NNNILabs/CC-CV-Linear-Power-Supply/KiCAD/comics_42-removebg-preview.png

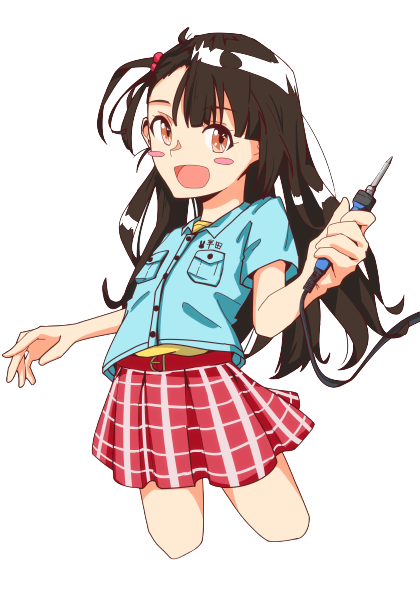
KiCAD/comics_42-removebg-preview.png
